juliancoy/AgnuQuena/site-hosting/public/assets/QuenaTube1.stl

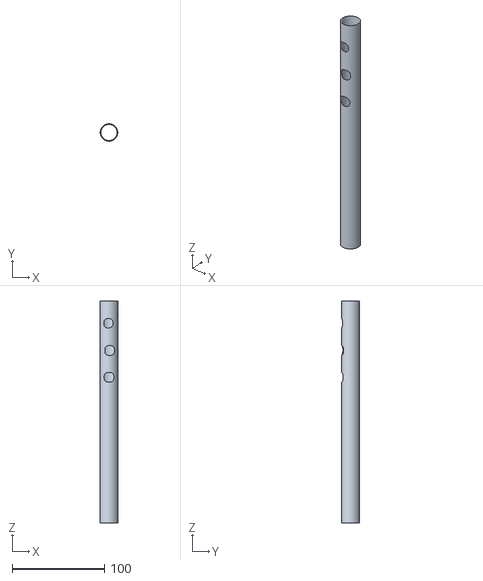
[picture p16: CAD file, 2026-08-04]
site-hosting/public/assets/QuenaTube1.stl
19.1 x 19.1 x 241.2
