juliancoy/AgnuQuena/website/assets/QuenaCaseEngraving.stl

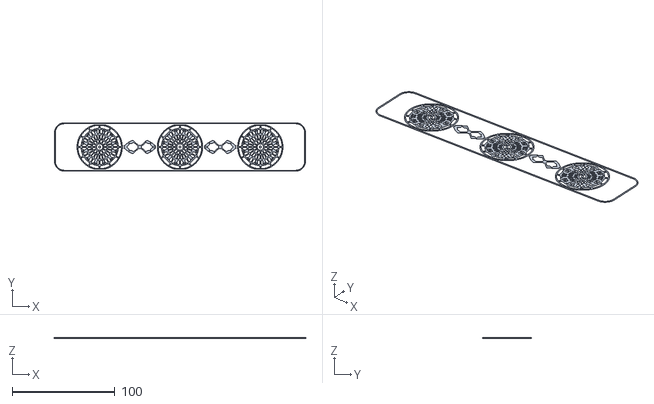
[picture p17: CAD file, 2026-08-04]
website/assets/QuenaCaseEngraving.stl
243.8 x 47.0 x 0.398
