juliancoy/AgnuQuena/bambu-slice-output/Quena.gcode.3mf

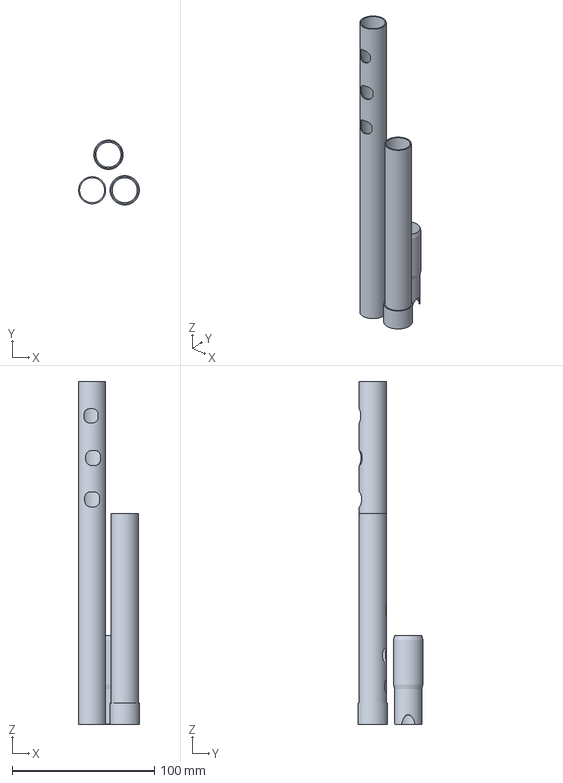
[picture p18: CAD file, 2026-08-17]
bambu-slice-output/Quena.gcode.3mf
42.8 x 45.7 x 241.2 mm
