juliancoy/AgnuQuena/website/assets/QuenaCaseArtwork.stl

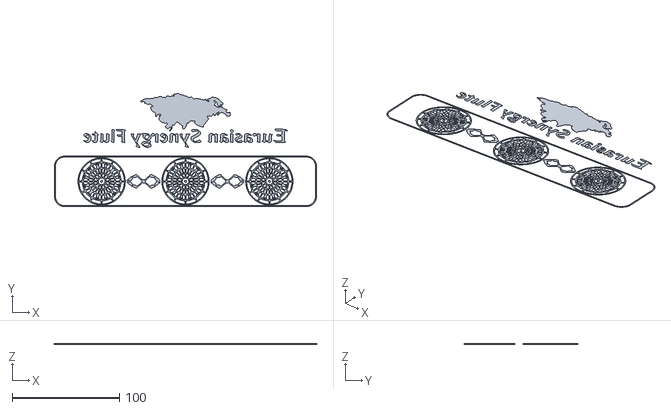
[picture p19: CAD file, 2026-08-04]
website/assets/QuenaCaseArtwork.stl
243.8 x 105.3 x 0.2
