juliancoy/AgnuQuena/QuenaPart3.stl

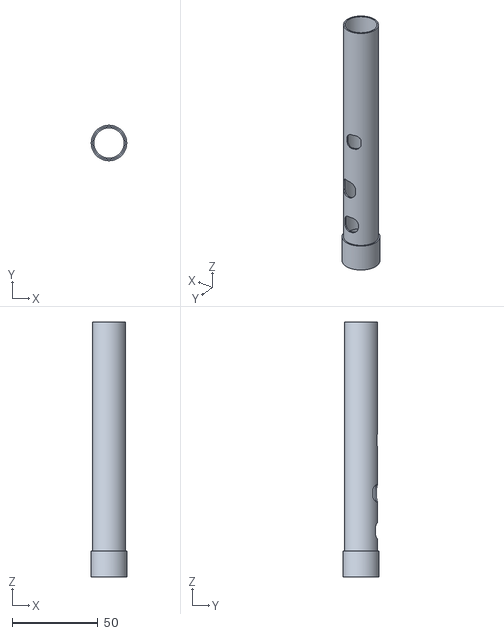
[picture p20: CAD file, 2026-08-04]
QuenaPart3.stl
20.7 x 20.7 x 148.4
