juliancoy/AgnuQuena/site-hosting/public/assets/QuenaCasePrintInPlace.stl

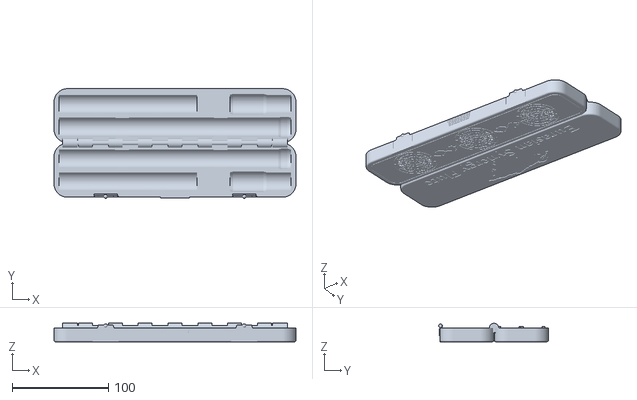
[picture p21: CAD file, 2026-08-04]
site-hosting/public/assets/QuenaCasePrintInPlace.stl
251.4 x 113.9 x 19.3
