juliancoy/AgnuQuena/website/assets/QuenaCaseTwoColorPrintInPlace.stl

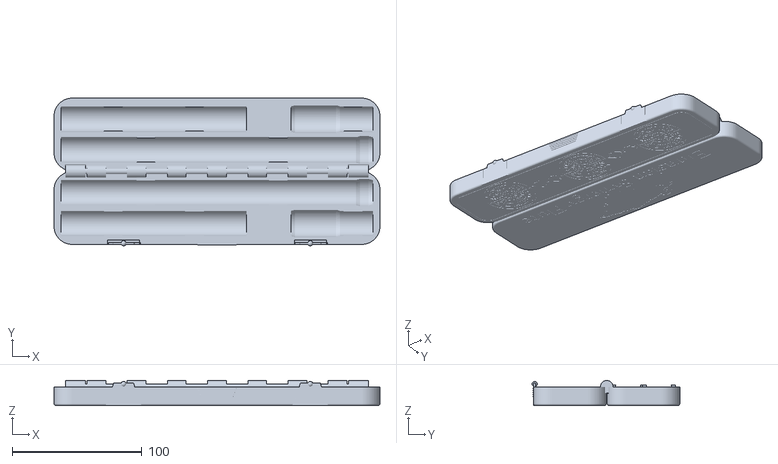
[picture p22: CAD file, 2026-08-04]
website/assets/QuenaCaseTwoColorPrintInPlace.stl
251.4 x 113.9 x 19.3
