juliancoy/AgnuQuena/site-hosting/public/assets/QuenaCaseBottomViewer.stl

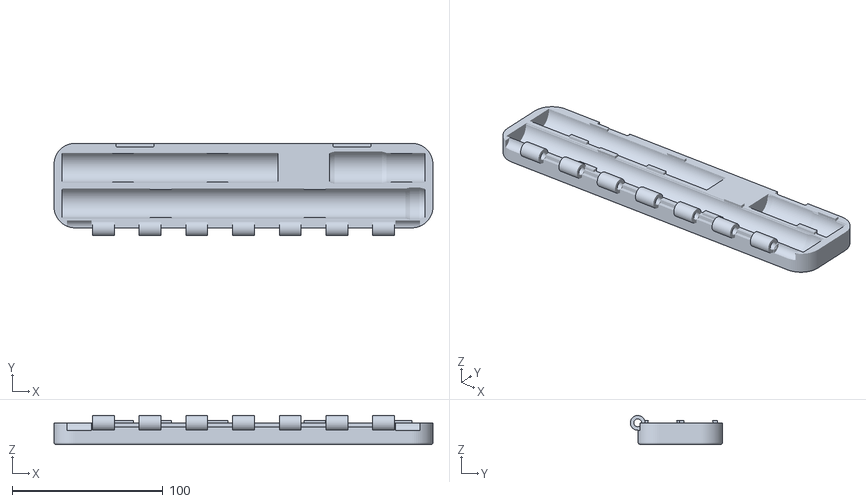
[picture p23: CAD file, 2026-08-03]
site-hosting/public/assets/QuenaCaseBottomViewer.stl
251.4 x 61.3 x 19.3
