juliancoy/AgnuQuena/site-hosting/public/assets/QuenaCaseLogo.stl

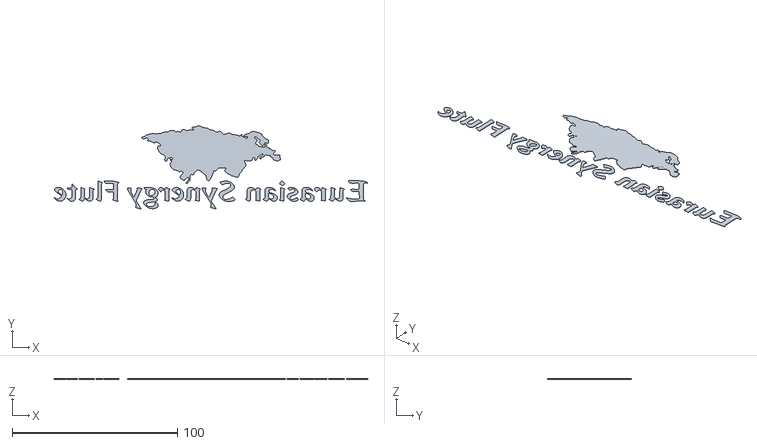
[picture p24: CAD file, 2026-08-02]
site-hosting/public/assets/QuenaCaseLogo.stl
190.0 x 50.6 x 0.6
