juliancoy/AgnuQuena/website/assets/QuenaMouthpiece.stl

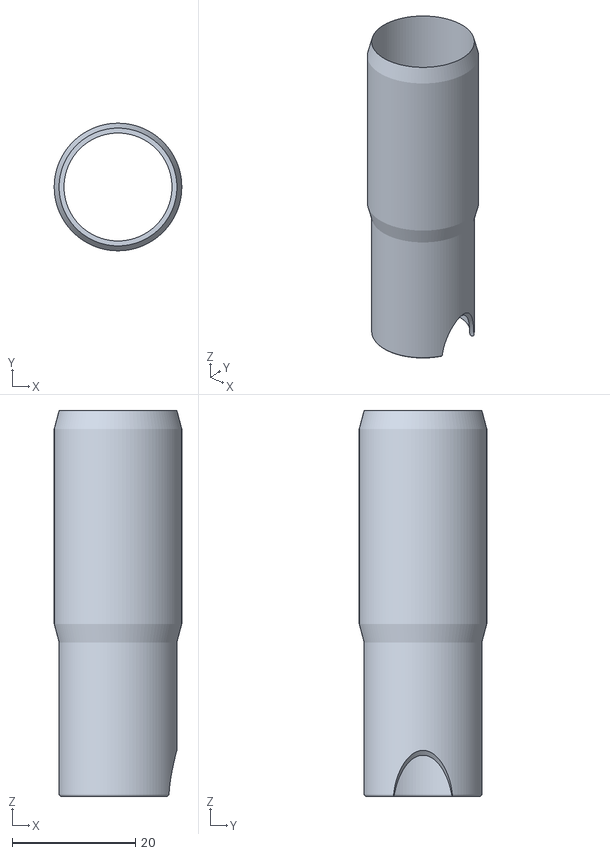
[picture p25: CAD file, 2026-08-02]
website/assets/QuenaMouthpiece.stl
20.7 x 20.7 x 62.6
