juliancoy/AgnuQuena/site-hosting/public/assets/QuenaCaseLatch.stl

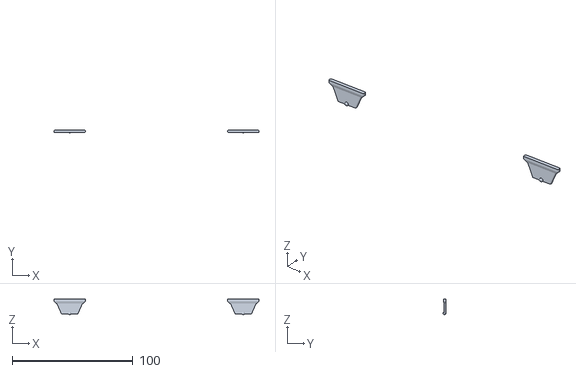
[picture p26: CAD file, 2026-07-22]
site-hosting/public/assets/QuenaCaseLatch.stl
170.0 x 2.60 x 12.9
