juliancoy/AgnuQuena/ToneHoleErgonomicCoupon.stl

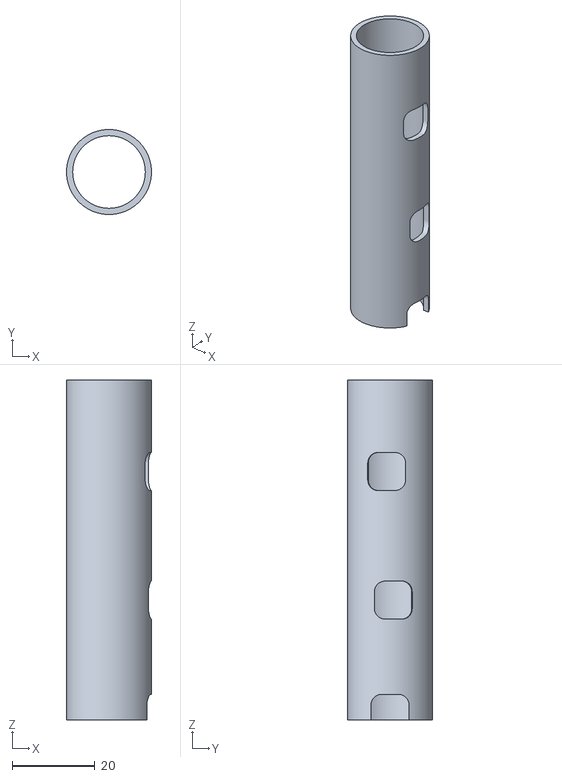
[picture p27: CAD file, 2026-07-27]
ToneHoleErgonomicCoupon.stl
20.5 x 20.5 x 82.0
