juliancoy/AgnuQuena/fipple02.stl

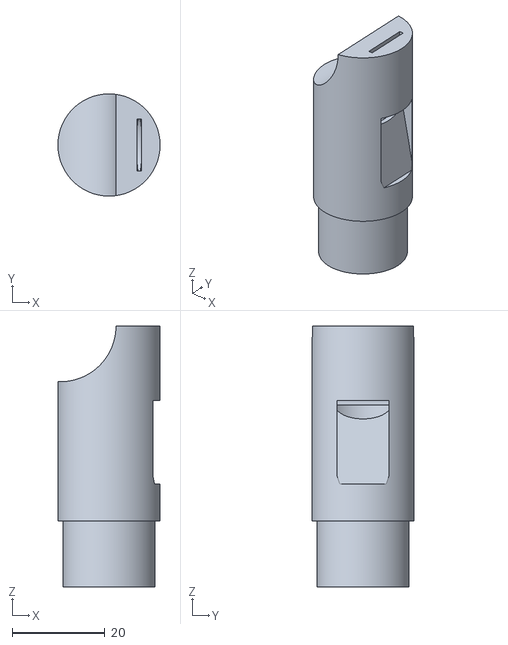
[picture p28: CAD file, 2026-07-22]
fipple02.stl
22.0 x 22.0 x 56.2
