juliancoy/AgnuQuena/Quena_fit_test.stl

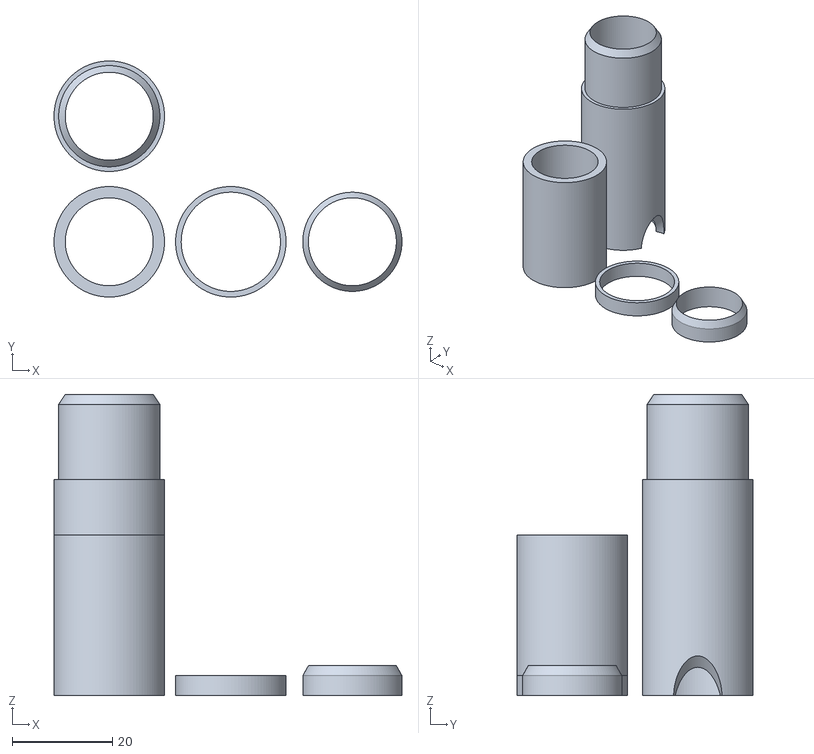
[picture p29: CAD file, 2025-10-19]
Quena_fit_test.stl
69.3 x 47.0 x 60.0
