juliancoy/AgnuQuena/q_mouthpiece.stl

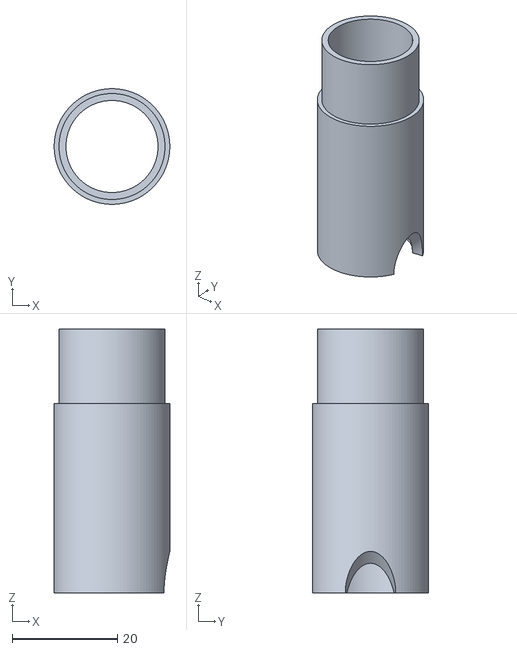
[picture p30: CAD file, 2025-10-19]
q_mouthpiece.stl
22.0 x 22.0 x 50.2
