juliancoy/AgnuQuena/QuenaCase.scad

// AgnuQuena carrying case
// Self-contained OpenSCAD model inspired by common hinged enclosure patterns:
// rounded shell, captive print-in-place hinge, snap clip, and fitted channels.

$fn = 64;

// Shared flute dimensions are generated from designs/quena.json.
include <generated/quena_parameters.scad>
include <generated/case_logo_dimensions.scad>

// Select "bottom", "mandala_panel", "lid", "case_engraving", "print_in_place",
// "print_in_place_two_color", "case_logo", "case_artwork_print", "latch",
// "assembly", "preview", or "none".
// Override from the CLI with:
// openscad -D 'part="print_in_place"' -o QuenaCasePrintInPlace.stl QuenaCase.scad
part = is_undef(part) ? "preview" : part;

// Case fit and print parameters.
// Close, printable fit around each part.  These are diametral/radial clearances;
// the separate axial clearance below controls end play.
part_clearance = 0.3;
connector_d = od + (shell_width + connector_radial_clearance) * 2;
channel_d = od + part_clearance * 2;
connector_channel_d = connector_d + part_clearance * 2;
max_channel_d = connector_channel_d;
axial_clearance = 0.6;
end_clearance = axial_clearance / 2;
// Keep the round cutter slightly proud of the nominal pocket ends.  This
// removes a coplanar cut face that can leave the cylindrical bore visibly
// stopping short of the terminal wall after tessellation/export.
bore_end_overlap = 0.08;
// Neighboring straight and tapered profile segments must overlap as solids;
// merely sharing an end face can leave open STL fragments at a raised lip.
profile_segment_overlap = 0.04;
// Match the broad shell exactly to the two perimeter paths in the bundled
// Bambu profile. Adjacent rounded-rectangle extrusions overlap by
// layer_height * (1 - PI/4), which is Bambu Studio's Flow::spacing() rule. A
// wall that falls between path counts makes the slicer weave slow gap fill
// between otherwise continuous perimeters.
outer_perimeter_width = 0.42;
inner_perimeter_width = 0.45;
slicing_layer_height = 0.2;
perimeter_path_overlap = slicing_layer_height * (1 - PI / 4);
wall = outer_perimeter_width + inner_perimeter_width - perimeter_path_overlap;
// Keep the original envelope and retain 3 mm of material only where the rim,
// hinge and friction-fit latch transfer load into the shell.
structural_margin = 3;
floor_thickness = 2.8;
lid_roof_thickness = 2.8;
// A broad plan-view radius removes the formerly abrupt luggage-case corners
// while leaving the straight hinge and latch lands unchanged.
corner_r = 14;
bed_edge_r = 1.5;

// Deep face-down recesses remain visible in single-filament prints. The
// two-color export below uses a separate one-layer recess and matching inlay.
mandala_inset = 5;
mandala_stroke = 0.9;
mandala_depth = 0.4;
mandala_radius = 22;
mandala_centers = [-78, 0, 78];
flourish_width = 30;
flourish_height = 12;

// The logo uses a deeper recess in single-filament mode for visibility.
logo_inlay_depth = 0.6;
// A single bed-facing layer is sufficient for the visible black artwork. The
// matching two-color shell closes directly over it on the following layer.
two_color_inlay_depth = 0.2;
logo_title_width = 190;
logo_map_width = 84;
logo_vertical_scale = 0.84;
logo_edge_margin = 2.0;

// Compact lands retain enough material between channels while keeping the
// diagonal P1S export inside a conservative 220 x 220 mm usable square.
row_gap = 2.5;
row_pitch = max_channel_d + row_gap;
// The longer mouthpiece connector still leaves a generous land while keeping
// the complete print-in-place case within the 256 mm target bed.
short_row_min_gap = 5.3;
channel_edge_land = 2.5;
// The main bed stops just past the tube equator; a continuous raised lip below
// reaches the light-snap height without making either complete shell taller.
equator_pass = 0.8;
flute_seat_depth = 0.5;
channel_deck_h = max_channel_d / 2 + equator_pass;
retention_lip_overrun = 3.0;
retention_ridge_wall = wall;
retention_ridge_root_overlap = 0.4;
retention_ridge_fusion_overlap = 0.04;
retention_lid_clearance = 0.25;
connector_backset = angled_transition_z + 2;
connector_expand_start = 2;
slot_lengths = [tube_part_1_length, tube_part_2_length, mouthpiece_total_length];
slot_names = ["TUBE 1", "TUBE 2", "MOUTH"];
// -1 places an outer sleeve before the stored body, +1 after it. The tube
// joint sleeve belongs to P2 and extends back over P1 when assembled.
slot_connector_sides = [0, -1, 1];
slot_has_connector = [false, true, true];
slot_connector_overlaps = [0, tube_joint_overlap, mouthpiece_overlap];
function connector_expand_end(i) =
    slot_connector_overlaps[i] - insert_z_tolerance - 2;
function connector_extra_l(i) = slot_connector_sides[i] < 0
    ? slot_connector_overlaps[i]
    : connector_expand_end(i) + angled_transition_z;
profile_lengths = [
    tube_part_1_length,
    tube_part_2_length + connector_extra_l(1),
    mouthpiece_total_length + connector_extra_l(2)
];
profile_max_ds = [channel_d, connector_channel_d, connector_channel_d];
// Each recess has only the specified total axial play, shared between its ends.
profile_cut_spans = [
    profile_lengths[0] + axial_clearance,
    profile_lengths[1] + axial_clearance,
    profile_lengths[2] + axial_clearance
];
profile_cut_center_offsets = [0, 0, 0];
short_row_min_length = profile_cut_spans[1] + profile_cut_spans[2]
    + short_row_min_gap * 3;
case_inner_l = max(
    profile_cut_spans[0] + channel_edge_land * 2,
    short_row_min_length
);
case_inner_w = row_pitch + max_channel_d + channel_edge_land * 2;
case_outer_l = case_inner_l + structural_margin * 2;
case_outer_w = case_inner_w + structural_margin * 2;
shell_inner_l = case_outer_l - wall * 2;
shell_inner_w = case_outer_w - wall * 2;
// Meet the raised bed directly against the shell's inner face.  A small
// overlap avoids a coplanar seam while keeping both printed edges aligned.
deck_shell_overlap = 0.04;
channel_deck_l = shell_inner_l + deck_shell_overlap * 2;
channel_deck_w = shell_inner_w + deck_shell_overlap * 2;
case_outer_h = floor_thickness + channel_deck_h;
lid_outer_h = case_outer_h;
// Seat every flute section 0.5 mm below the nominal half-depth.  The raised
// channel edges therefore wrap just past the equator and lightly grip it.
slot_z = floor_thickness + max_channel_d / 2 - flute_seat_depth;

rim_h = 2.4;
rim_wall = 1.4;
rim_clearance = 0.6;
lid_z_clearance = 0.3;

lid_closed_z = case_outer_h + lid_z_clearance;

// Print-in-place hinge. In the production pose both shell exteriors lie on the
// bed, opened 180 degrees. The lid carries a continuous axle captured inside
// seven closed bottom bearings, with eight alternating lid webs tying the axle
// back to the lid. No post-print pin or snap assembly is required.
hinge_axle_d = 4.6;
// The lid rotates 180 degrees into the print pose, so its source-space axle top
// becomes printer-facing. The bearing remains fully round and starts from a
// short body-side web rather than a visible flat.
hinge_axle_print_flat = 0.60;
hinge_bearing_starter_h = 0.40;
hinge_bearing_clearance = 0.60;
hinge_bearing_bore_d = hinge_axle_d + hinge_bearing_clearance;
hinge_bearing_outer_d = 9.8;
hinge_segment_w = 14.5;
hinge_segment_gap = 1.0;
hinge_segment_pitch = hinge_segment_w + hinge_segment_gap;
// A 0.60 mm separation between the two rear shell edges prevents the halves
// from fusing on the first layer in the side-by-side production pose.
hinge_print_shell_gap = 0.60;
hinge_body_inset = 4.6;
hinge_axis_y = -case_outer_w / 2 - hinge_bearing_outer_d / 2 + hinge_body_inset;
// Put the pivot on the center of the clearance plane between equal-height
// halves.  This keeps the hinge neutral instead of biasing it toward the lid.
hinge_axis_z = case_outer_h + lid_z_clearance / 2;
hinge_bearing_segments = [
    for (i = [-6 : 2 : 6])
        [i * hinge_segment_pitch - hinge_segment_w / 2,
         i * hinge_segment_pitch + hinge_segment_w / 2]
];
hinge_axle_support_segments = [
    for (i = [-7 : 2 : 7])
        [i * hinge_segment_pitch - hinge_segment_w / 2,
         i * hinge_segment_pitch + hinge_segment_w / 2]
];
hinge_axle_x1 = hinge_axle_support_segments[0][0];
hinge_axle_x2 = hinge_axle_support_segments[
    len(hinge_axle_support_segments) - 1
][1];
hinge_span = hinge_axle_x2 - hinge_axle_x1;
hinge_tab_t = 2.2;
// Carry the shell's plan-view curvature into each shorter hinge base at the
// same radius-to-width ratio. This rounds the visible axial shoulders without
// expanding the shallow radial land into the stationary case half.
hinge_base_r = corner_r * hinge_segment_w / case_outer_l;
// Solid lid-owned barrels cover both exposed axle ends. Their cylindrical
// exterior has no print flat; a short axial overhang leaves each visible end
// as a complete round face rather than a D-shaped axle stub.
hinge_end_barrel_d = hinge_bearing_outer_d;
hinge_end_barrel_overhang = 1.2;

front_pull_w = 48;
front_pull_depth = 3.6;
front_pull_h = 2.2;
front_pull_y = case_outer_w / 2 + front_pull_depth / 2 - 0.4;
bottom_pull_z = lid_closed_z - front_pull_h - 0.25;
lid_pull_z = front_pull_h;

latch_clip_w = 56;
latch_clip_depth = 7.5;
latch_clip_wall = 2.0;
latch_clip_r = 0.8;
latch_clip_clearance = 0.35;
latch_clip_lead_in = 1.0;
latch_clip_grip_rib_w = 3.0;
latch_clip_bridge_y = front_pull_y + front_pull_depth / 2 + latch_clip_wall / 2 + latch_clip_clearance;
latch_clip_jaw_y = -(latch_clip_depth / 2 - latch_clip_wall / 2);
latch_clip_bottom_z = bottom_pull_z - latch_clip_wall - latch_clip_clearance;
latch_clip_top_jaw_z = lid_closed_z + lid_pull_z + front_pull_h + latch_clip_clearance;
latch_clip_top_offset = latch_clip_top_jaw_z - latch_clip_bottom_z;
latch_clip_total_h = latch_clip_top_offset + latch_clip_wall;
latch_nub_d = 3.0;
latch_nub_l = 2.6;
latch_nub_tip_l = 0.7;
latch_nub_tip_r = 0.35;
latch_socket_clearance = 0.4;
latch_socket_d = latch_nub_d + latch_socket_clearance;
latch_socket_depth = 3.8;
latch_knuckle_outer_d = 6.6;
latch_knuckle_gap = 1.6;
latch_install_flex_span = latch_clip_w;
latch_carrier_t = 1.6;
latch_carrier_h = 5.6;
latch_axis_z = latch_clip_bottom_z + latch_clip_total_h / 2;
latch_mount_x = latch_clip_w / 2 + latch_knuckle_gap;

// Integral radial snap latch. Two lid axles press into open C-knuckles on the
// bottom; the knuckle lips, not a long lid carrier, provide the compliance.
latch_snap_nub_d = 3.2;
latch_snap_socket_clearance = 0.30;
latch_snap_socket_d = latch_snap_nub_d + latch_snap_socket_clearance;
latch_snap_outer_d = 7.0;
latch_snap_throat = 2.7;
latch_snap_knuckle_w = 8.0;
latch_snap_lip_t = 1.4;
latch_snap_lip_l = 7.0;
latch_snap_lead = 1.2;
latch_snap_pair_x = 19;
latch_snap_axis_y = case_outer_w / 2 + 6.5;
latch_snap_axis_z = lid_closed_z + 2.0;

// Compact harmonica-case style ball snaps.
latch_ball_d = 3.4;
latch_ball_neck_d = 2.6;
latch_cup_bore_d = 3.15;
latch_cup_cavity_d = 3.75;
latch_cup_outer_d = 7.0;
latch_cup_h = 5.2;
latch_cup_slot_w = 1.2;
latch_cup_lip_t = 1.4;
latch_cup_flex_l = 5.2;
latch_pair_x = 19;
latch_center_y = case_outer_w / 2 + 4.5;
latch_center_z = lid_closed_z + 1.0;

// Final simple harmonica-case latch: one lid tongue, one shallow nub, and one
// shallow recess in the bottom front wall.
latch_tongue_w = 18.0;
latch_tongue_t = 1.6;
latch_tongue_flex_l = 15.9;
latch_tongue_y = case_outer_w / 2 - latch_tongue_t / 2;
latch_nub_r = 2.0;
latch_nub_protrusion = 1.25;
latch_indent_depth = 0.85;
latch_release_deflection = latch_nub_protrusion - latch_indent_depth;
latch_nub_z = case_outer_h - 2.05;
latch_point_xs = [-72, 72];
latch_point_count = 2;
latch_tongue_tip_w = 15.5;
latch_tongue_root_w = 24.0;
latch_tongue_root_blend_h = 4.4;
thumb_grip_w = 30;
thumb_grip_rib_h = 0.75;
thumb_grip_rib_depth = 0.45;
thumb_grip_rib_count = 5;
thumb_grip_z0 = 0.8;
thumb_grip_pitch = 1.55;

module smooth_latch_tongue(xc, local_y, bottom_z) {
    slice_h = 1.4;
    hull() {
        translate([xc, local_y, bottom_z])
            rounded_box([
                latch_tongue_tip_w,
                latch_tongue_t,
                slice_h
            ], 0.7);
        translate([xc, local_y,
            bottom_z + latch_tongue_flex_l - slice_h])
            rounded_box([
                latch_tongue_root_w,
                latch_tongue_t,
                slice_h
            ], 0.7);
    }
    // A shallow, wider shoulder overlaps the case wall and removes the hard
    // visual/mechanical corner at the tongue root.
    hull() {
        translate([xc, local_y,
            bottom_z + latch_tongue_flex_l - latch_tongue_root_blend_h])
            rounded_box([
                latch_tongue_root_w,
                latch_tongue_t,
                latch_tongue_root_blend_h
            ], 0.8);
        translate([xc, local_y - 0.35,
            bottom_z + latch_tongue_flex_l - 0.5])
            rounded_box([
                latch_tongue_root_w + 4,
                latch_tongue_t + 0.7,
                1.8
            ], 0.9);
    }
}

module lid_thumb_grip() {
    // Five low rounded ribs centered between the two latches. Their shallow
    // profile is printable without support but provides a clear tactile pull
    // target for a thumb or fingertip.
    for (i = [0 : thumb_grip_rib_count - 1])
        translate([
            0,
            case_outer_w / 2 + thumb_grip_rib_depth / 2 - 0.08,
            thumb_grip_z0 + i * thumb_grip_pitch
        ]) rounded_box([
            thumb_grip_w - i * 1.2,
            thumb_grip_rib_depth,
            thumb_grip_rib_h
        ], thumb_grip_rib_h / 2);
}

// Align the short-row pockets to the P1 pocket ends: P2's sleeved end uses
// P1's left edge, and the mouthpiece connector uses P1's right edge.
p1_cut_left = -profile_cut_spans[0] / 2;
p1_cut_right = profile_cut_spans[0] / 2;
short_tube_cut_center = p1_cut_left + profile_cut_spans[1] / 2;
mouth_cut_center = p1_cut_right - profile_cut_spans[2] / 2;
slot_xs = [
    // Keep the longest tube body centered axially.  Its connector and free-end
    // clearances remain intentionally asymmetric inside the channel profile.
    0,
    short_tube_cut_center - profile_cut_center_offsets[1],
    mouth_cut_center + profile_cut_center_offsets[2]
];
slot_ys = [-row_pitch / 2, row_pitch / 2, row_pitch / 2];
slot_rot_zs = [0, 0, 180];

function slot_x(i) = slot_xs[i];
function slot_y(i) = slot_ys[i];
function slot_rot_z(i) = slot_rot_zs[i];
function profile_l(i) = profile_lengths[i];
function profile_d(i) = profile_max_ds[i];
function body_x0(i) = -profile_l(i) / 2
    + (slot_connector_sides[i] < 0 ? connector_extra_l(i) : 0);
function body_x1(i) = body_x0(i) + slot_lengths[i];
function connector_x0(i) = body_x0(i)
    - (slot_connector_sides[i] < 0 ? connector_extra_l(i) : 0);
function connector_x1(i) = body_x1(i)
    + (slot_connector_sides[i] > 0 ? connector_extra_l(i) : 0);
function profile_x0(i) = slot_connector_sides[i] < 0
    ? connector_x0(i)
    : body_x0(i);
function profile_x1(i) = slot_connector_sides[i] > 0
    ? connector_x1(i)
    : body_x1(i);
module rounded_box(size, r) {
    hull() {
        for (x = [-size[0] / 2 + r, size[0] / 2 - r])
        for (y = [-size[1] / 2 + r, size[1] / 2 - r])
            translate([x, y, 0])
                cylinder(h = size[2], r = r);
    }
}

module y_extruded_rounded_box(size, r) {
    translate([0, -size[1] / 2, 0])
        rotate([-90, 0, 0])
            linear_extrude(height = size[1])
                rounded_rect_2d([size[0], size[2]], r);
}

module fully_rounded_box(size, r, edge_r = bed_edge_r) {
    minkowski() {
        translate([0, 0, edge_r])
            linear_extrude(height = size[2] - 2 * edge_r)
                rounded_rect_2d(
                    [size[0] - 2 * edge_r, size[1] - 2 * edge_r],
                    max(0.01, r - edge_r)
                );
        sphere(r = edge_r);
    }
}

module bed_rounded_box(size, r, round_bottom = false, round_top = false) {
    union() {
        fully_rounded_box(size, r);
        if (!round_bottom)
            rounded_box([size[0], size[1], bed_edge_r], r);
        if (!round_top)
            translate([0, 0, size[2] - bed_edge_r])
                rounded_box([size[0], size[1], bed_edge_r], r);
    }
}

module rounded_rect_2d(size, r) {
    hull()
        for (x = [-size[0] / 2 + r, size[0] / 2 - r])
        for (y = [-size[1] / 2 + r, size[1] / 2 - r])
            translate([x, y]) circle(r = r);
}

module ring_2d(radius, stroke = mandala_stroke) {
    difference() {
        circle(r = radius + stroke / 2);
        circle(r = max(0.01, radius - stroke / 2));
    }
}

module radial_stroke_2d(y1, y2, stroke = mandala_stroke) {
    hull()
        for (y = [y1, y2])
            translate([0, y]) circle(d = stroke);
}

module stroke_path_2d(points, stroke = mandala_stroke) {
    for (i = [0 : len(points) - 2])
        hull()
            for (p = [points[i], points[i + 1]])
                translate(p) circle(d = stroke);
}

module flourish_leaf_2d(length = 4.8, width = 2.2) {
    scale([length / 2, width / 2]) circle(r = 1);
}

module flourish_2d() {
    // Four mirrored tendrils and broad leaves fill the spaces between the
    // rosettes without introducing unsupported islands or nozzle hairlines.
    union() {
        rotate(45) square([2.8, 2.8], center = true);
        for (sx = [-1, 1])
            for (sy = [-1, 1])
                scale([sx, sy]) {
                    stroke_path_2d([
                        [0, 0], [3, 2.5], [7, flourish_height / 2],
                        [11, 4], [flourish_width / 2, 0.8], [12, -1.2]
                    ]);
                    translate([7.8, 4.7]) rotate(-18)
                        flourish_leaf_2d();
                    translate([12.1, 1.8]) rotate(-42)
                        flourish_leaf_2d(4.2, 2.0);
                }
    }
}

module mandala_2d(radius = mandala_radius, petals = 12) {
    // Concentric rings, orbiting halos, and alternating radial rays create a
    // deterministic rosette with no imported artwork or fragile hairlines.
    union() {
        for (scale = [0.16, 0.34, 0.57, 0.80, 0.98])
            ring_2d(radius * scale);
        circle(d = mandala_stroke * 2.2);
        for (angle = [0 : 360 / petals : 359])
            rotate(angle) {
                radial_stroke_2d(radius * 0.18, radius * 0.94);
                translate([0, radius * 0.68])
                    ring_2d(radius * 0.145, mandala_stroke * 0.82);
            }
        for (angle = [360 / petals / 2 : 360 / petals : 359])
            rotate(angle)
                radial_stroke_2d(
                    radius * 0.38,
                    radius * 0.75,
                    mandala_stroke * 0.82
                );
    }
}

module mandala_panel_2d() {
    border_radius = corner_r - mandala_inset;
    inner_margin = mandala_inset + mandala_stroke + 0.6;
    union() {
        // The frame centerline follows the case edge exactly 5 mm inward.
        difference() {
            rounded_rect_2d(
                [
                    case_outer_l - 2 * mandala_inset + mandala_stroke,
                    case_outer_w - 2 * mandala_inset + mandala_stroke
                ],
                border_radius + mandala_stroke / 2
            );
            rounded_rect_2d(
                [
                    case_outer_l - 2 * mandala_inset - mandala_stroke,
                    case_outer_w - 2 * mandala_inset - mandala_stroke
                ],
                border_radius - mandala_stroke / 2
            );
        }
        intersection() {
            union() {
                for (x = mandala_centers)
                    translate([x, 0]) mandala_2d();
                for (i = [0 : len(mandala_centers) - 2])
                    translate([
                        (mandala_centers[i] + mandala_centers[i + 1]) / 2,
                        0
                    ]) flourish_2d();
            }
            rounded_rect_2d(
                [
                    case_outer_l - 2 * inner_margin,
                    case_outer_w - 2 * inner_margin
                ],
                max(0.01, corner_r - inner_margin)
            );
        }
    }
}

module lid_ornament_recess(depth = mandala_depth) {
    translate([0, 0, lid_outer_h - depth])
        linear_extrude(height = depth + 0.01)
            mandala_panel_2d();
}

module lid_ornament_inlay(depth = mandala_depth) {
    intersection() {
        translate([0, 0, lid_outer_h - depth])
            linear_extrude(height = depth)
                mandala_panel_2d();
        lid_assembly(false);
    }
}

module case_logo_2d() {
    // These vectors are traced from the selected two-colour PNG. The vertical
    // scale retains the long lid composition while leaving a real edge margin.
    // Rotate in the shell plane so the artwork reads normally when viewed
    // through the bottom shell's exterior (-Z) face. Do not reflect it: that
    // would leave the title and continent backward.
    intersection() {
        rotate(180)
            scale([1, logo_vertical_scale])
                union() {
                translate([0, 20])
                    translate([
                        -logo_title_width / 2,
                        -logo_title_width
                            * logo_title_source_size[1]
                            / logo_title_source_size[0] / 2
                    ])
                        resize([logo_title_width, 0], auto = true)
                            import("generated/case_logo_title.svg");
                translate([0, -9])
                    translate([
                        -logo_map_width / 2,
                        -logo_map_width
                            * logo_map_source_size[1]
                            / logo_map_source_size[0] / 2
                    ])
                        resize([logo_map_width, 0], auto = true)
                            import("generated/case_logo_map.svg");
            }
        rounded_rect_2d(
            [
                case_outer_l - 2 * logo_edge_margin,
                case_outer_w - 2 * logo_edge_margin
            ],
            max(0.01, corner_r - logo_edge_margin)
        );
    }
}

module bottom_logo_inlay(depth = logo_inlay_depth) {
    translate([0, 0, 0])
        linear_extrude(height = depth)
            case_logo_2d();
}

module bottom_logo_recess(depth = logo_inlay_depth) {
    // Extend only through the exterior face. The recess roof stays exactly at
    // the inlay top so the two ABS materials fuse instead of leaving a gap.
    translate([0, 0, -0.01])
        linear_extrude(height = depth + 0.01)
            case_logo_2d();
}

module profiled_segment(x1, x2, d1, d2) {
    translate([(x1 + x2) / 2, 0, 0])
        rotate([0, 90, 0])
            cylinder(
                h = x2 - x1 + profile_segment_overlap * 2,
                d1 = d1,
                d2 = d2,
                center = true
            );
}

module stored_profile_envelope(
    i,
    normal_d,
    expanded_d,
    terminal_extension = 0
) {
    x0 = body_x0(i);
    x1 = body_x1(i);
    side = slot_connector_sides[i];

    if (side < 0) {
        cx0 = connector_x0(i);
        profiled_segment(
            cx0 - terminal_extension,
            x0,
            expanded_d,
            expanded_d
        );
        profiled_segment(x0, x1 + terminal_extension, normal_d, normal_d);
    } else if (side > 0) {
        cx1 = connector_x1(i);
        profiled_segment(x0 - terminal_extension, x1 - connector_backset, normal_d, normal_d);
        profiled_segment(
            x1 - connector_backset,
            x1 - connector_expand_start,
            normal_d,
            expanded_d
        );
        profiled_segment(
            x1 - connector_expand_start,
            x1 + connector_expand_end(i),
            expanded_d,
            expanded_d
        );
        profiled_segment(x1 + connector_expand_end(i), cx1, expanded_d, normal_d);
        profiled_segment(cx1, cx1 + terminal_extension, normal_d, normal_d);
    } else {
        profiled_segment(
            x0 - terminal_extension,
            x1 + terminal_extension,
            normal_d,
            normal_d
        );
    }
}

module profiled_channel_cut(
    i,
    extra_depth = 0,
    flat_relief = true,
    diameter_offset = 0
) {
    cut_x0 = profile_x0(i) - end_clearance;
    cut_x1 = profile_x1(i) + end_clearance;

    union() {
        stored_profile_envelope(
            i,
            channel_d + diameter_offset,
            connector_channel_d + diameter_offset,
            end_clearance + bore_end_overlap
        );

        // Open only the material above the cradle lip.  The relief must begin
        // at equator_pass, not below the tube centerline, so the cylindrical
        // sidewall remains curved all the way to its just-past-equator top.
        // The lid omits this relief and retains its matching cylindrical cut.
        if (flat_relief) {
            relief_h = profile_d(i) / 2 + extra_depth;
            translate([
                (cut_x0 + cut_x1) / 2,
                0,
                equator_pass + relief_h / 2
            ])
                cube([
                    cut_x1 - cut_x0,
                    profile_d(i) + diameter_offset,
                    relief_h
                ], center = true);
        }
    }
}

module all_channel_cuts(extra_depth = 0, flat_relief = true) {
    for (i = [0 : 2])
        translate([slot_x(i), slot_y(i), slot_z])
            rotate([0, 0, slot_rot_z(i)])
                profiled_channel_cut(i, extra_depth, flat_relief);
}

module retention_ridge_local(i, cavity = false) {
    clearance = cavity ? retention_lid_clearance : 0;
    local_z0 = case_outer_h - slot_z
        - retention_ridge_root_overlap - clearance;
    local_z1 = retention_lip_overrun + clearance;
    ridge_l = profile_cut_spans[i]
        + 2 * (retention_ridge_wall + clearance);
    ridge_w = profile_d(i)
        + 2 * (retention_ridge_wall + clearance);

    module ridge_envelope() {
        translate([0, 0, (local_z0 + local_z1) / 2])
            cube([ridge_l, ridge_w, local_z1 - local_z0], center = true);
    }

    if (cavity) {
        // The lid already removes the complete cylindrical tube channel.
        // Removing the expanded outer envelope here gives every transition
        // positive clearance without reproducing coplanar profile faces.
        ridge_envelope();
    } else difference() {
        ridge_envelope();
        // Overlap the bottom lip into the existing cradle by 0.02 mm radially
        // so the two regions remain one printable solid.
        translate([retention_ridge_fusion_overlap / 2, 0, 0])
            profiled_channel_cut(
                i,
                0,
                false,
                -2 * clearance - retention_ridge_fusion_overlap
            );
    }
}

module retention_border(cavity = false) {
    for (i = [0 : 2])
        translate([slot_x(i), slot_y(i), slot_z])
            rotate([0, 0, slot_rot_z(i)])
                retention_ridge_local(i, cavity);
}

module lid_retention_relief() {
    translate([0, 0, -lid_closed_z]) retention_border(true);
}

// Nominal solid envelopes for collision and fit validation.  These follow the
// stored flute bodies and expanded connector regions, without channel
// clearance, and are intentionally independent of preview-only geometry.
module stored_part_proxy(i) {
    stored_profile_envelope(i, od, connector_d);
}

module stored_parts_proxy() {
    for (i = [0 : 2])
        translate([slot_x(i), slot_y(i), slot_z])
            rotate([0, 0, slot_rot_z(i)])
                stored_part_proxy(i);
}

module bottom_channel_deck() {
    // One continuous bed forms every half-cylinder cradle and meets the shell
    // directly; do not leave an open moat between their vertical edges.
    difference() {
        translate([0, 0, floor_thickness])
            rounded_box(
                [channel_deck_l, channel_deck_w, channel_deck_h],
                max(corner_r - wall + deck_shell_overlap, 1)
            );
        all_channel_cuts(channel_deck_h + 1);
    }
}

module x_cylinder_between(x1, x2, d) {
    translate([(x1 + x2) / 2, 0, 0])
        rotate([0, 90, 0])
            cylinder(h = x2 - x1, d = d, center = true);
}

module hinge_tab(x1, x2, local_z, seam_side = -1) {
    attach_y = -case_outer_w / 2 + 0.4;

    translate([
        (x1 + x2) / 2,
        (hinge_axis_y + attach_y) / 2,
        local_z + seam_side * hinge_tab_t / 2
    ])
        y_extruded_rounded_box(
            [x2 - x1, attach_y - hinge_axis_y, hinge_tab_t],
            hinge_base_r
        );
}

module hinge_axle_at(
    x1,
    x2,
    local_y,
    local_z,
    d = hinge_axle_d,
    flat_side = 0,
    print_flat = hinge_axle_print_flat
) {
    if (flat_side == 0) {
        translate([0, local_y, local_z]) x_cylinder_between(x1, x2, d);
    } else {
        r = d / 2;
        cutoff_z = local_z + flat_side * (r - print_flat);
        keep_h = d + 2;
        keep_center_z = flat_side > 0
            ? cutoff_z - keep_h / 2
            : cutoff_z + keep_h / 2;
        intersection() {
            translate([0, local_y, local_z])
                x_cylinder_between(x1, x2, d);
            translate([(x1 + x2) / 2, local_y, keep_center_z])
                cube([x2 - x1 + 0.2, d + 2, keep_h], center = true);
        }
    }
}

module hinge_bearing_bore_at(x1, x2, local_y, local_z) {
    translate([0, local_y, local_z])
        x_cylinder_between(x1, x2, hinge_bearing_bore_d);
}

module hinge_bearing_at(x1, x2, local_y, local_z) {
    difference() {
        translate([0, local_y, local_z])
            x_cylinder_between(x1, x2, hinge_bearing_outer_d);
        hinge_bearing_bore_at(
            x1 - 0.2, x2 + 0.2, local_y, local_z
        );
    }
}

module bottom_hinge_starter_web(x1, x2, local_z) {
    // This shallow tangent web gives the first circular bearing layers a path
    // back to the shell. It sits entirely below the running bore, so the
    // encircling bearing surface remains visually and mechanically round.
    bearing_bottom = local_z - hinge_bearing_outer_d / 2;
    attach_y = -case_outer_w / 2 + 0.4;
    web_w = x2 - x1;

    hull() {
        translate([
            (x1 + x2) / 2,
            hinge_axis_y,
            bearing_bottom + hinge_bearing_starter_h / 2
        ]) cube([web_w, 0.4, hinge_bearing_starter_h], center = true);
        translate([
            (x1 + x2) / 2,
            attach_y,
            bearing_bottom + 0.5
        ]) cube([web_w, 0.4, 1.0], center = true);
    }
}

module bottom_hinge() {
    for (segment = hinge_bearing_segments) {
        difference() {
            union() {
                bottom_hinge_starter_web(
                    segment[0], segment[1], hinge_axis_z
                );
                hinge_bearing_at(
                    segment[0], segment[1], hinge_axis_y, hinge_axis_z
                );
            }
            hinge_bearing_bore_at(
                segment[0] - 0.2,
                segment[1] + 0.2,
                hinge_axis_y,
                hinge_axis_z
            );
        }
    }
}

module lid_outer_end_barrels(clearance = 0) {
    first = hinge_axle_support_segments[0];
    last = hinge_axle_support_segments[
        len(hinge_axle_support_segments) - 1
    ];
    d = hinge_end_barrel_d + clearance * 2;

    translate([0, hinge_axis_y, hinge_axis_z - lid_closed_z]) {
        x_cylinder_between(
            first[0] - hinge_end_barrel_overhang - clearance,
            first[1] + clearance,
            d
        );
        x_cylinder_between(
            last[0] - clearance,
            last[1] + hinge_end_barrel_overhang + clearance,
            d
        );
    }
}

module lid_hinge() {
    local_axis_z = hinge_axis_z - lid_closed_z;
    hinge_axle_at(
        hinge_axle_x1,
        hinge_axle_x2,
        hinge_axis_y,
        local_axis_z,
        hinge_axle_d,
        1
    );
    lid_outer_end_barrels();
    for (segment = hinge_axle_support_segments)
        hinge_tab(segment[0], segment[1], local_axis_z, 1);
}

module lid_bottom_hinge_relief() {
    local_axis_z = hinge_axis_z - lid_closed_z;
    relief_clearance = 0.3;
    // Follow the fixed stator's round envelope. The bearing intersects the
    // rear shell directly, so no square backer or oversized corner relief is
    // needed behind it.
    relief_d = hinge_bearing_outer_d + relief_clearance * 2;

    for (segment = hinge_bearing_segments)
        translate([0, hinge_axis_y, local_axis_z])
            x_cylinder_between(
                segment[0] - relief_clearance,
                segment[1] + relief_clearance,
                relief_d
            );

    // Once the pivot is recessed, the rounded top-rear edge of the bottom
    // also sweeps through the lid between and beyond the bearing segments.
    // Clear that small radius continuously; the separate bearing pockets
    // above remain responsible for the individual round stators.
    seam_sweep_r = sqrt(
        pow(-case_outer_w / 2 - hinge_axis_y, 2)
        + pow(case_outer_h - hinge_axis_z, 2)
    ) + relief_clearance + 0.2;
    translate([0, hinge_axis_y, local_axis_z])
        x_cylinder_between(
            -case_outer_l / 2 - 4,
            case_outer_l / 2 + 4,
            seam_sweep_r * 2
        );
}

module lid_hinge_relief() {
    // The recessed lid axle and its webs occupy part of the bottom rear wall
    // when the case is closed. Clear its complete swept cross-section through the top
    // of that wall, with a small FDM allowance, instead of allowing the two
    // case halves to fuse geometrically.
    relief_clearance = 0.3;
    relief_y = hinge_axle_d + relief_clearance * 2;
    relief_bottom = hinge_axis_z - hinge_axle_d / 2 - relief_clearance;
    relief_h = case_outer_h - relief_bottom + 0.02;

    // The axle is continuous between its end webs, so its circular sweep must
    // be relieved continuously from the bottom rear wall as well.
    translate([
        (hinge_axle_x1 + hinge_axle_x2) / 2,
        hinge_axis_y,
        relief_bottom + relief_h / 2
    ])
        cube([
            hinge_axle_x2 - hinge_axle_x1 + relief_clearance * 2,
            relief_y,
            relief_h
        ], center = true);

    // The two lid-owned end barrels replace the formerly exposed axle stubs.
    // Clear their complete round exterior from the bottom rear wall.
    translate([0, 0, lid_closed_z])
        lid_outer_end_barrels(relief_clearance);
}

module front_pull(local_z = bottom_pull_z) {
    translate([0, front_pull_y, local_z])
        rounded_box([front_pull_w, front_pull_depth, front_pull_h], 1.4);
}

module latch_entry_bevels() {
    for (z = [
        latch_clip_wall + latch_clip_lead_in / 2,
        latch_clip_top_offset - latch_clip_lead_in / 2
    ])
        translate([
            0,
            latch_clip_jaw_y - latch_clip_depth / 2 + latch_clip_lead_in / 2,
            z
        ])
            rotate([45, 0, 0])
                cube([
                    latch_clip_w + 0.4,
                    latch_clip_lead_in * 2.5,
                    latch_clip_lead_in
                ], center = true);
}

module latch_grip_ribs() {
    rib_z0 = latch_clip_wall + 1.0;
    rib_h = latch_clip_total_h - latch_clip_wall * 2 - 2.0;

    for (x = [-latch_clip_w / 2 + 10, 0, latch_clip_w / 2 - 10])
        translate([x, latch_carrier_t / 2 + latch_clip_r / 2 - 0.2, rib_z0])
            rounded_box([latch_clip_grip_rib_w, latch_clip_r, rib_h], latch_clip_r / 2);
}

module latch_clip_core() {
    difference() {
        union() {
            translate([0, latch_clip_jaw_y, 0])
                rounded_box([latch_clip_w, latch_clip_depth, latch_clip_wall], latch_clip_r);
            translate([0, latch_clip_jaw_y, latch_clip_top_offset])
                rounded_box([latch_clip_w, latch_clip_depth, latch_clip_wall], latch_clip_r);
            rounded_box([latch_clip_w, latch_carrier_t, latch_clip_total_h], latch_clip_r);
            latch_grip_ribs();
        }
        latch_entry_bevels();
    }
}

module latch_clip() {
    translate([0, latch_clip_bridge_y, latch_clip_bottom_z])
        union() {
            latch_clip_core();
            latch_nub_pair();
        }
}

module latch_nub_pair(local_y = latch_carrier_t / 2,
                      local_z = latch_clip_total_h / 2) {
    left_root = -latch_clip_w / 2;
    right_root = latch_clip_w / 2;
    left_tip = left_root - latch_nub_l;
    right_tip = right_root + latch_nub_l;
    translate([0, local_y - 0.2, local_z]) {
        hull() {
            translate([left_tip + latch_nub_tip_r, 0, 0]) sphere(r = latch_nub_tip_r);
            x_cylinder_between(left_tip + latch_nub_tip_l - 0.15,
                left_tip + latch_nub_tip_l + 0.15, latch_nub_d);
        }
        x_cylinder_between(left_tip + latch_nub_tip_l - 0.25, left_root + 3.0, latch_nub_d);
        x_cylinder_between(right_root - 3.0, right_tip - latch_nub_tip_l + 0.25, latch_nub_d);
        hull() {
            x_cylinder_between(right_tip - latch_nub_tip_l - 0.15,
                right_tip - latch_nub_tip_l + 0.15, latch_nub_d);
            translate([right_tip - latch_nub_tip_r, 0, 0]) sphere(r = latch_nub_tip_r);
        }
    }
}

module lid_integral_latch() {
    local_axis_z = latch_axis_z - lid_closed_z;
    carrier_h = latch_carrier_h;

    // The lid-side bridge is the spring. Pulling its center outward bows it
    // across X, shortening the nub span so both nubs clear the bottom sockets.
    union() {
        translate([0, latch_clip_bridge_y, local_axis_z])
            rounded_box([latch_clip_w, latch_carrier_t, carrier_h], latch_clip_r);
        translate([0, latch_clip_bridge_y, 0])
            latch_nub_pair(latch_carrier_t / 2, local_axis_z);
        for (x = [-latch_clip_w / 2 + 5, latch_clip_w / 2 - 5])
            hull() {
                translate([x, front_pull_y, lid_pull_z + front_pull_h / 2])
                    sphere(r = 1.4);
                translate([x, latch_clip_bridge_y, local_axis_z + carrier_h / 2 - 0.7])
                    sphere(r = 1.4);
            }
    }
}

module latch_snap_axle(xc, local_z) {
    translate([0, latch_snap_axis_y, local_z])
        x_cylinder_between(
            xc - latch_snap_knuckle_w / 2,
            xc + latch_snap_knuckle_w / 2,
            latch_snap_nub_d
        );
}

module bottom_latch_knuckle(xc) {
    socket_r = latch_snap_socket_d / 2;
    lip_y = socket_r + latch_snap_lip_t / 2;
    top_z = latch_snap_axis_z + latch_snap_lip_l;

    difference() {
        union() {
            translate([0, latch_snap_axis_y, latch_snap_axis_z])
                x_cylinder_between(
                    xc - latch_snap_knuckle_w / 2,
                    xc + latch_snap_knuckle_w / 2,
                    latch_snap_outer_d
                );
            for (side = [-1, 1])
                hull() {
                    translate([
                        xc,
                        latch_snap_axis_y + side * lip_y,
                        latch_snap_axis_z + latch_snap_outer_d / 4
                    ]) cube([
                        latch_snap_knuckle_w,
                        latch_snap_lip_t,
                        latch_snap_outer_d / 2
                    ], center = true);
                    translate([
                        xc,
                        latch_snap_axis_y + side * (lip_y + latch_snap_lead),
                        top_z
                    ]) cube([
                        latch_snap_knuckle_w,
                        latch_snap_lip_t,
                        0.8
                    ], center = true);
                }
        }
        translate([0, latch_snap_axis_y, latch_snap_axis_z])
            x_cylinder_between(
                xc - latch_snap_knuckle_w / 2 - 0.1,
                xc + latch_snap_knuckle_w / 2 + 0.1,
                latch_snap_socket_d
            );
        translate([
            xc,
            latch_snap_axis_y,
            latch_snap_axis_z + latch_snap_lip_l / 2 + 0.1
        ]) cube([
            latch_snap_knuckle_w + 0.4,
            latch_snap_throat,
            latch_snap_lip_l + latch_snap_outer_d
        ], center = true);
    }

    // Low web transfers pull load into the bottom front rail.
    hull() {
        translate([xc, front_pull_y, bottom_pull_z]) sphere(r = 1.5);
        translate([
            xc,
            latch_snap_axis_y,
            latch_snap_axis_z - latch_snap_outer_d / 2 + 0.8
        ]) sphere(r = 1.5);
    }
}

module bottom_radial_latch() {
    for (xc = [-latch_snap_pair_x, latch_snap_pair_x])
        bottom_latch_knuckle(xc);
}

module lid_radial_latch() {
    local_axis_z = latch_snap_axis_z - lid_closed_z;
    for (xc = [-latch_snap_pair_x, latch_snap_pair_x]) {
        support_x = xc - sign(xc) * (latch_snap_knuckle_w / 2 + 3.0);
        translate([0, latch_snap_axis_y, local_axis_z])
            x_cylinder_between(
                xc < 0 ? xc - latch_snap_knuckle_w / 2 : support_x,
                xc < 0 ? support_x : xc + latch_snap_knuckle_w / 2,
                latch_snap_nub_d
            );
        hull() {
            translate([support_x, front_pull_y, lid_pull_z + front_pull_h / 2])
                sphere(r = 1.5);
            translate([support_x, latch_snap_axis_y, local_axis_z])
                sphere(r = latch_snap_nub_d / 2);
        }
    }
}

module bottom_harmonica_latch() {
    for (xc = [-latch_pair_x, latch_pair_x]) {
        difference() {
            union() {
                translate([xc, latch_center_y,
                    latch_center_z - latch_cup_h / 2])
                    cylinder(h = latch_cup_h, d = latch_cup_outer_d);
                hull() {
                    translate([xc, front_pull_y, bottom_pull_z]) sphere(r = 1.5);
                    translate([xc, latch_center_y,
                        latch_center_z - latch_cup_h / 2 + 0.8]) sphere(r = 1.5);
                }
            }
            translate([xc, latch_center_y, latch_center_z])
                sphere(d = latch_cup_cavity_d);
            translate([xc, latch_center_y, latch_center_z])
                cylinder(h = latch_cup_h / 2 + 0.1, d = latch_cup_bore_d);
            // One outward split lets the cup expand without weakening both
            // attachment roots.
            translate([xc, latch_center_y + latch_cup_outer_d / 2,
                latch_center_z])
                cube([latch_cup_slot_w, latch_cup_outer_d,
                    latch_cup_h + 0.4], center = true);
        }
    }
}

module lid_harmonica_latch() {
    local_z = latch_center_z - lid_closed_z;
    for (xc = [-latch_pair_x, latch_pair_x]) {
        translate([xc, latch_center_y, local_z])
            sphere(d = latch_ball_d);
        translate([xc, latch_center_y, local_z + latch_ball_d / 2 - 0.1])
            cylinder(h = 2.2, d = latch_ball_neck_d);
        hull() {
            translate([xc, front_pull_y, lid_pull_z + front_pull_h / 2])
                sphere(r = 1.4);
            translate([xc, latch_center_y, local_z + latch_ball_d / 2 + 1.2])
                sphere(r = 1.3);
        }
    }
}

module lid_simple_latch_tongues() {
    local_nub_z = latch_nub_z - lid_closed_z;
    tongue_bottom_z = local_nub_z - 0.6;

    for (xc = latch_point_xs)
        smooth_latch_tongue(xc, latch_tongue_y, tongue_bottom_z);
}

module lid_simple_latch_nubs() {
    local_nub_z = latch_nub_z - lid_closed_z;
    inner_y = latch_tongue_y - latch_tongue_t / 2;

    for (xc = latch_point_xs)
        translate([
            xc,
            inner_y + latch_nub_r - latch_nub_protrusion,
            local_nub_z
        ]) sphere(r = latch_nub_r);
}

module lid_simple_latch() {
    lid_simple_latch_tongues();
    lid_simple_latch_nubs();
}

module bottom_simple_latch_indent_cut() {
    // Include the rounded root shoulder, which blends 0.35 mm farther inward
    // than the tongue itself, plus closing clearance at the centered hinge.
    pocket_depth = latch_tongue_t + 1.0;
    pocket_base_y = case_outer_w / 2 - pocket_depth;
    for (xc = latch_point_xs) {
        // Receive the complete tongue thickness so its outside face is flush
        // with the uninterrupted front edge of the closed case.
        translate([
            xc,
            case_outer_w / 2 - pocket_depth / 2 + 0.1,
            latch_nub_z - 3.0
        ]) rounded_box([
            latch_tongue_root_w + 1.0,
            pocket_depth + 0.2,
            latch_tongue_flex_l + 1.0
        ], 0.8);
        translate([
            xc,
            pocket_base_y + latch_nub_r - latch_indent_depth,
            latch_nub_z
        ]) sphere(r = latch_nub_r + 0.05);
    }
}

module lid_simple_latch_relief_cuts() {
    local_nub_z = latch_nub_z - lid_closed_z;
    relief_bottom = local_nub_z - 0.9;
    relief_h = latch_tongue_flex_l - latch_tongue_root_blend_h;
    for (xc = latch_point_xs) {
        // Side slots define the cantilever; the wider upper shoulder remains
        // joined to the lid and carries the bending load into the shell.
        for (side = [-1, 1])
            translate([
                xc + side * (latch_tongue_root_w / 2 + 0.35),
                case_outer_w / 2 - structural_margin / 2,
                relief_bottom
            ]) cube([0.7, structural_margin + 1.0, relief_h]);
        // Hidden pocket behind the tongue provides outward release travel.
        translate([
            xc - latch_tongue_root_w / 2 - 0.4,
            case_outer_w / 2 - structural_margin - 0.2,
            relief_bottom
        ]) cube([
            latch_tongue_root_w + 0.8,
            structural_margin - latch_tongue_t + 0.25,
            relief_h
        ]);
    }
}

module latch_socket_knuckles() {
    socket_y = latch_clip_bridge_y + latch_carrier_t / 2;
    for (side = [-1, 1]) {
        inner_x = side * latch_mount_x;
        outer_x = side * (latch_mount_x + latch_socket_depth);
        x1 = min(inner_x, outer_x);
        x2 = max(inner_x, outer_x);
        union() {
          difference() {
            translate([0, socket_y, latch_axis_z])
                x_cylinder_between(x1, x2, latch_knuckle_outer_d);
            translate([0, socket_y, latch_axis_z])
                x_cylinder_between(x1 - 0.1, x2 + 0.1, latch_socket_d);
          }
          hull() {
            translate([side * (front_pull_w / 2 - 3.0),
                front_pull_y, bottom_pull_z]) sphere(r = 1.3);
            translate([side * (latch_mount_x + latch_socket_depth / 2),
                socket_y, latch_axis_z - 3.0]) sphere(r = 1.2);
          }
        }
    }
}

module bottom_rim() {
    translate([0, 0, case_outer_h])
    difference() {
        rounded_box([case_outer_l - structural_margin * 1.4, case_outer_w - structural_margin * 1.4, rim_h], max(corner_r - structural_margin, 1));
        translate([0, 0, -0.01])
            rounded_box([
                case_outer_l - structural_margin * 1.4 - rim_wall * 2,
                case_outer_w - structural_margin * 1.4 - rim_wall * 2,
                rim_h + 0.02
            ], max(corner_r - structural_margin - rim_wall, 1));
    }
}

module lid_rim_socket() {
    translate([0, 0, -0.01])
    difference() {
        rounded_box([
            case_outer_l - structural_margin * 1.4 + rim_clearance * 2,
            case_outer_w - structural_margin * 1.4 + rim_clearance * 2,
            rim_h + 0.02
        ], max(corner_r - structural_margin + rim_clearance, 1));
        translate([0, 0, -0.01])
            rounded_box([
                case_outer_l - structural_margin * 1.4 - rim_wall * 2 - rim_clearance * 2,
                case_outer_w - structural_margin * 1.4 - rim_wall * 2 - rim_clearance * 2,
                rim_h + 0.04
            ], max(corner_r - structural_margin - rim_wall - rim_clearance, 1));
    }
}

module bottom_latch_receiver_reinforcement() {
    // The friction-fit tongue intentionally collides with its indent.  Keep
    // the old 3 mm receiver thickness locally so tightening the broad shell
    // cannot shave off either the indent or the mating nub.
    receiver_w = latch_tongue_root_w + 1.0;
    for (xc = latch_point_xs)
        translate([
            xc - receiver_w / 2,
            case_outer_w / 2 - structural_margin,
            floor_thickness
        ]) cube([
            receiver_w,
            structural_margin - wall + 0.02,
            case_outer_h - floor_thickness
        ]);
}

module bottom_case_core(
    with_logo_recess = true,
    logo_depth = logo_inlay_depth
) {
    difference() {
        union() {
            difference() {
                union() {
                    bed_rounded_box(
                        [case_outer_l, case_outer_w, case_outer_h],
                        corner_r,
                        round_bottom = true
                    );
                }
                translate([0, 0, floor_thickness])
                    rounded_box(
                        [shell_inner_l, shell_inner_w, case_outer_h + 2],
                        max(corner_r - wall, 1)
                    );
                all_channel_cuts(4);
            }
            bottom_channel_deck();
            bottom_latch_receiver_reinforcement();
            retention_border();
        }
        // Apply the moving lid envelope after the complete bottom interior is
        // assembled so neither the shell nor the raised channel bed can touch
        // the axle or its round end barrels.
        lid_hinge_relief();
        if (with_logo_recess) bottom_logo_recess(logo_depth);
    }
}

module bottom_case(with_logo_recess = true, logo_depth = logo_inlay_depth) {
    bottom_case_core(with_logo_recess, logo_depth);
}

module bottom_assembly(with_logo_recess = true, logo_depth = logo_inlay_depth) {
    difference() {
        union() {
            bottom_case(with_logo_recess, logo_depth);
            bottom_hinge();
        }
        bottom_simple_latch_indent_cut();
    }
}

module lid_case(
    with_ornament_recess = true,
    ornament_depth = mandala_depth
) {
    // The two case halves have identical outside height.  Their meeting faces
    // are flat; no tongue, ridge, or receiving groove crosses the seam.
    lid_h = lid_outer_h;

    difference() {
        bed_rounded_box(
            [case_outer_l, case_outer_w, lid_h],
            corner_r,
            round_top = true
        );
        translate([0, 0, -lid_closed_z])
            all_channel_cuts(4, false);
        lid_retention_relief();
        if (with_ornament_recess) lid_ornament_recess(ornament_depth);
    }
}

module lid_assembly(
    with_ornament_recess = true,
    ornament_depth = mandala_depth
) {
    union() {
        // The bottom-knuckle clearance belongs to the lid shell only.  Keep
        // it out of the hinge union so it cannot square-cut the rounded pins.
        difference() {
            union() {
                lid_case(with_ornament_recess, ornament_depth);
                lid_simple_latch_tongues();
                lid_thumb_grip();
            }
            lid_bottom_hinge_relief();
            lid_simple_latch_relief_cuts();
        }
        // Add the complete spherical nubs after every subtractive operation.
        // The tongue pocket must never flatten or hollow their inner faces.
        lid_simple_latch_nubs();
        lid_hinge();
    }
}

module labels() {
    for (i = [0 : 2])
        translate([slot_x(i) - profile_l(i) / 2 + 3, slot_y(i), case_outer_h + 0.25])
            linear_extrude(height = 0.6)
                text(slot_names[i], size = 5, halign = "left", valign = "center");
}

module preview_ghosts() {
    color([0.1, 0.1, 0.1, 0.28])
    for (i = [0 : 2])
        translate([slot_x(i), slot_y(i), slot_z])
            rotate([0, 0, slot_rot_z(i)])
                profiled_channel_cut(i);
}

module closed_assembly_case() {
    bottom_assembly();
    translate([0, 0, lid_closed_z])
        lid_assembly();
}

module lid_in_print_pose() {
    translate([0, hinge_axis_y, hinge_axis_z])
        rotate([180, 0, 0])
            translate([
                0,
                -hinge_axis_y,
                -(hinge_axis_z - lid_closed_z)
            ]) children();
}

module case_artwork_in_print_pose(depth = two_color_inlay_depth) {
    bottom_logo_inlay(depth);
    lid_in_print_pose() lid_ornament_inlay(depth);
}

module print_in_place_case(
    logo_depth = logo_inlay_depth,
    ornament_depth = mandala_depth
) {
    // Rotate the closed lid exactly 180 degrees about the production hinge.
    // This puts both exterior backs at Z=0 and leaves the two rear shell edges
    // separated by hinge_print_shell_gap on the build plate.
    bottom_assembly(true, logo_depth);
    lid_in_print_pose() lid_assembly(true, ornament_depth);
}

if (part == "none") {
} else if (part == "bottom") {
    bottom_assembly();
} else if (part == "mandala_panel") {
    mandala_panel_2d();
} else if (part == "lid") {
    lid_assembly();
} else if (part == "case_engraving") {
    lid_ornament_inlay();
} else if (part == "case_logo") {
    bottom_logo_inlay();
} else if (part == "case_artwork_print") {
    case_artwork_in_print_pose();
} else if (part == "latch") {
    lid_simple_latch();
} else if (part == "assembly") {
    closed_assembly_case();
} else if (part == "print_in_place_two_color") {
    print_in_place_case(two_color_inlay_depth, two_color_inlay_depth);
} else if (part == "print_in_place") {
    print_in_place_case();
} else {
    color("steelblue") bottom_assembly();
    labels();
    translate([0, 0, lid_closed_z])
        color("lightgray") lid_assembly();
    translate([0, 0, lid_closed_z])
        color("gold") lid_ornament_inlay();
    color("gold") bottom_logo_inlay();
    preview_ghosts();
}
