juliancoy/AgnuQuena/acoustics/assembled_air.scad

use <../Quena.scad>

assembled_air_volume();
