juliancoy/AgnuQuena/acoustics/assembled_quena.scad

use <../Quena.scad>

mouthpiece();
piecewise_vert();
