juliancoy/AgnuQuena/generated/case_logo_dimensions.scad

// Generated by tools/vectorize_case_logo.py; do not edit.
logo_title_source_size = [1129, 124];
logo_map_source_size = [1194, 595];
