juliancoy/AgnuQuena/analysis/quena_structural.scad

// Continuous production tone-hole tube used for structural FEA exports.
use <../Quena.scad>

tube();
