juliancoy/AgnuQuena/QuenaCaseAssembly_9views.png

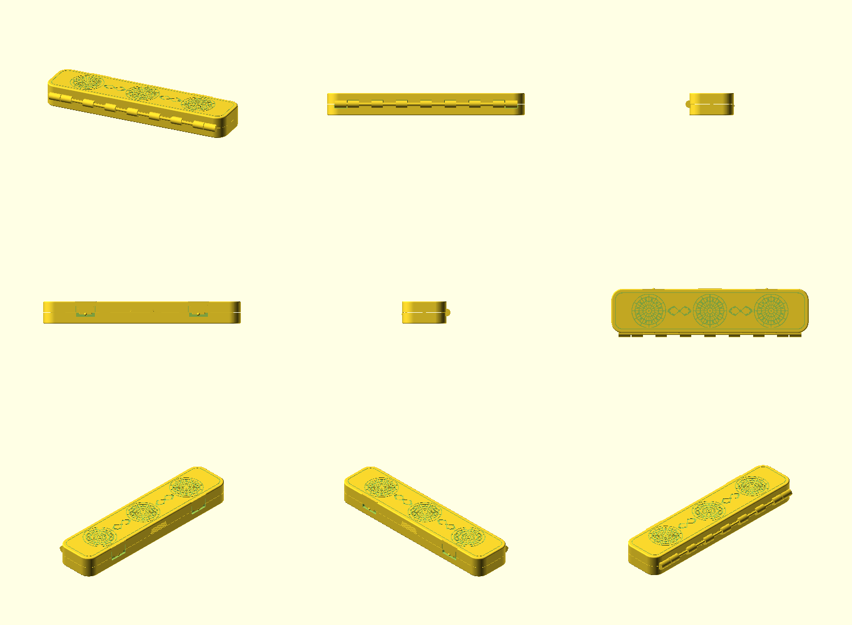
QuenaCaseAssembly_9views.png
