juliancoy/AgnuQuena/QuenaCasePrintInPlace_9views.png

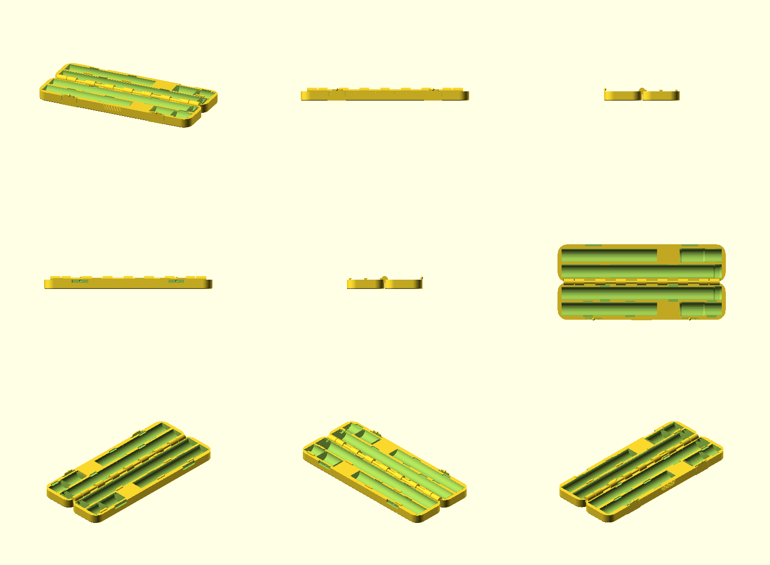
QuenaCasePrintInPlace_9views.png
